tamu-edu-students/ECEN404_403_Team_33_Pollination_Monitoring-Internal/pi_program/sample1.jpg

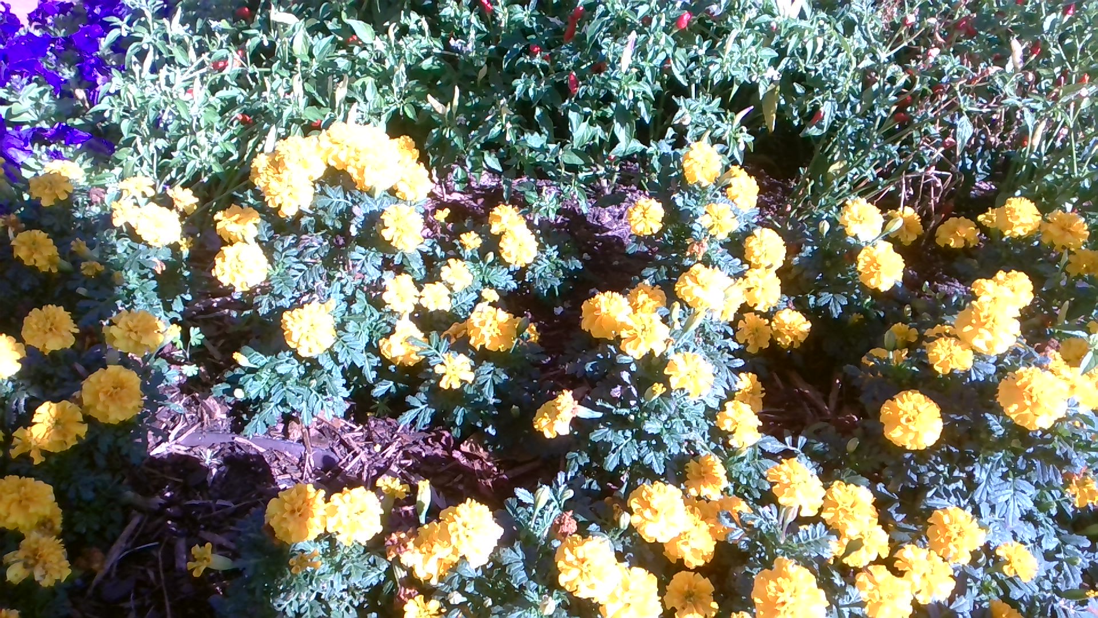
pi_program/sample1.jpg
