tamu-edu-students/ECEN404_403_Team_33_Pollination_Monitoring-Internal/lidar_client_communication/generated_heatmaps/heatmap_04-16-2026_15.20.06.001.png

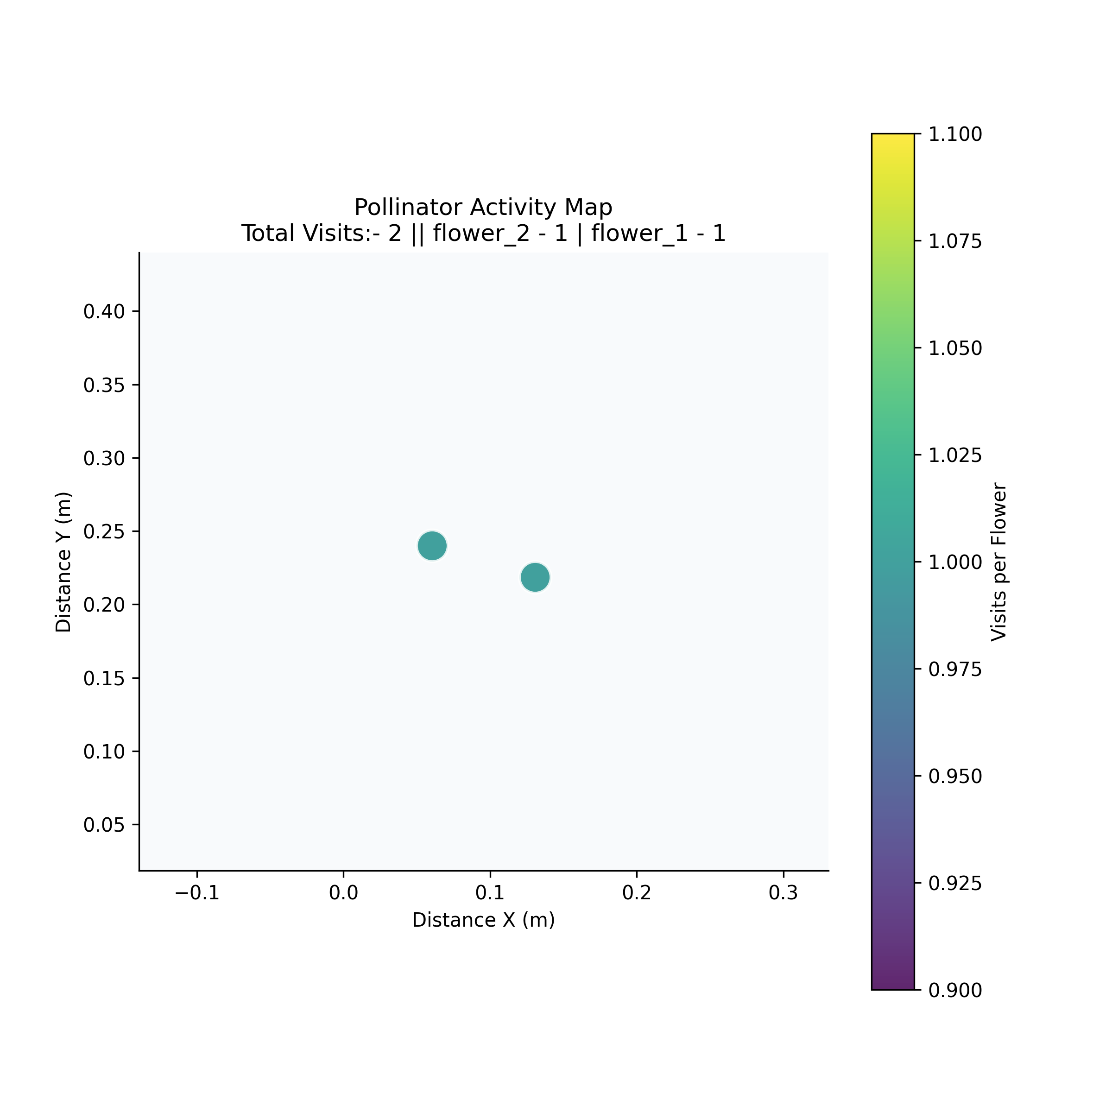
lidar_client_communication/generated_heatmaps/heatmap_04-16-2026_15.20.06.001.png
