tamu-edu-students/ECEN404_403_Team_33_Pollination_Monitoring-Internal/lidar_ML/dataset/dataset_report.png

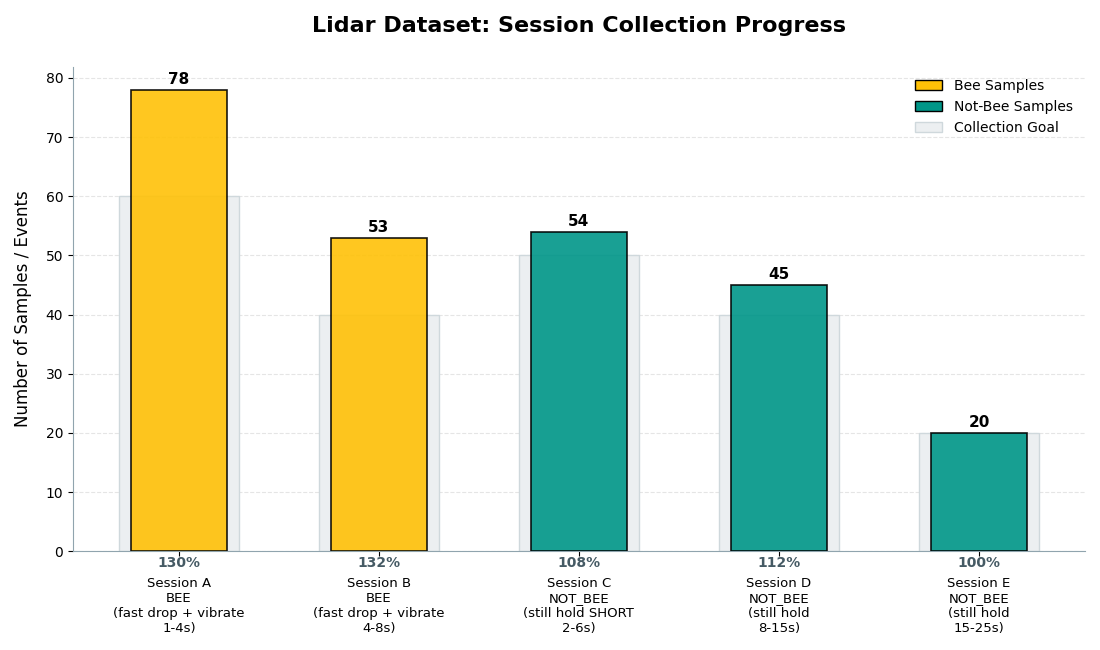
lidar_ML/dataset/dataset_report.png
